svofski/library-for-ants/bloh/gripor1.jpg

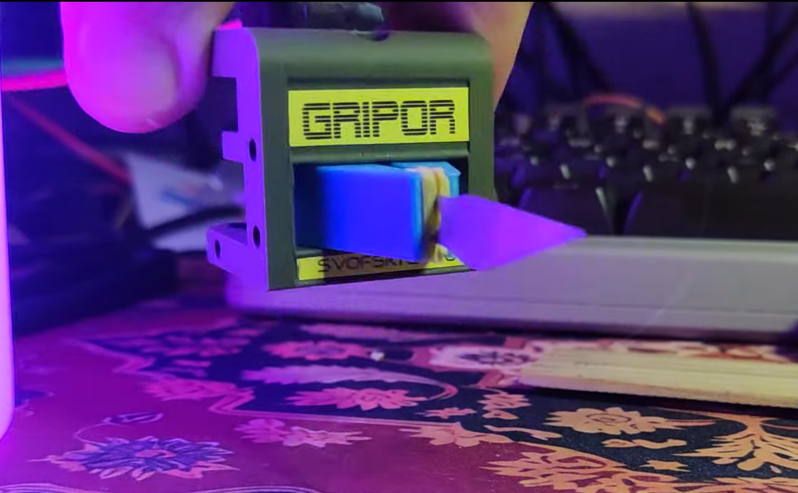
bloh/gripor1.jpg
