svofski/library-for-ants/bloh/gripor2.jpg

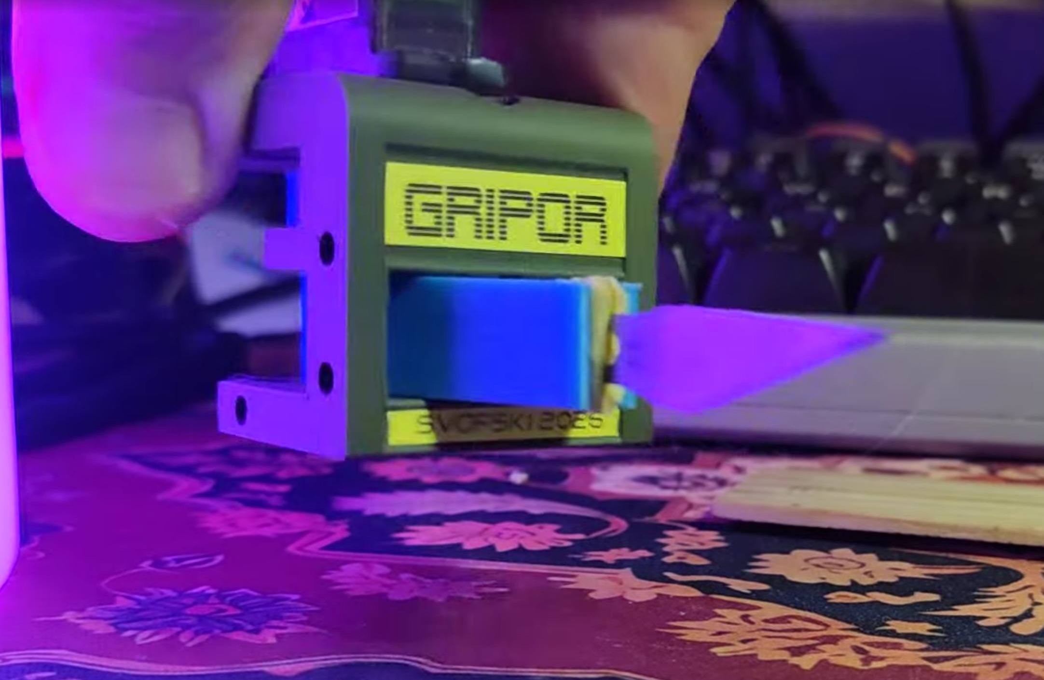
bloh/gripor2.jpg
