svofski/library-for-ants/bloh/IMG_20260404_140003.jpg

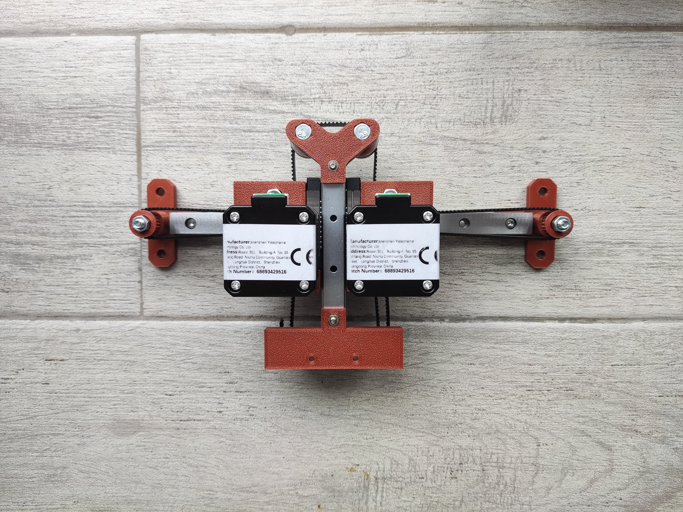
bloh/IMG_20260404_140003.jpg
