svofski/library-for-ants/bloh/IMG_20260531_192031.jpg

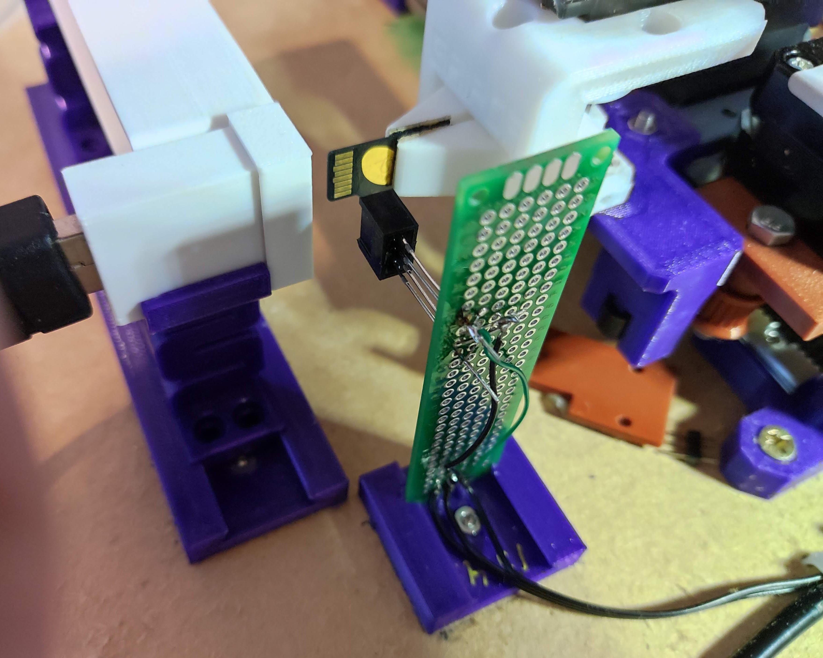
bloh/IMG_20260531_192031.jpg
