svofski/library-for-ants/bloh/IMG_20260725_130940.jpg

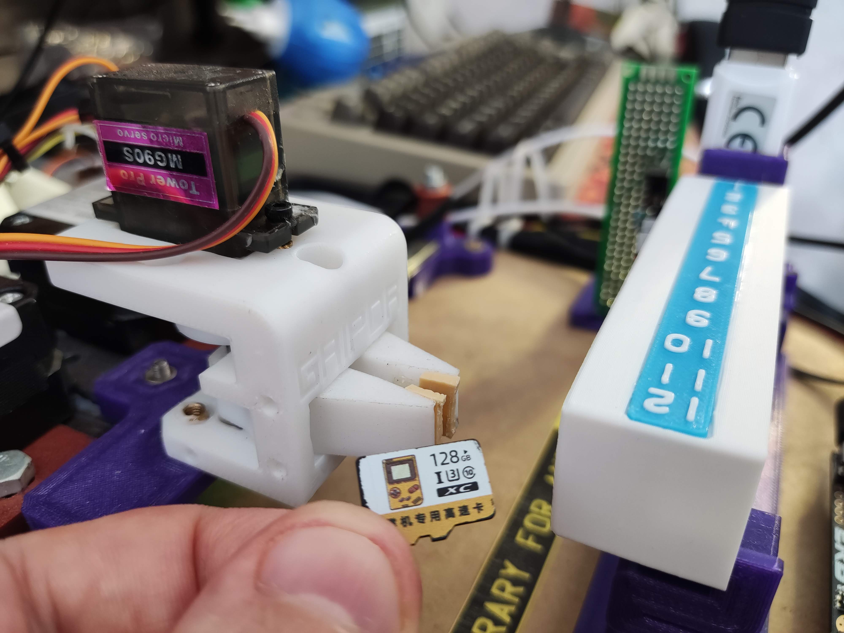
bloh/IMG_20260725_130940.jpg
