svofski/library-for-ants/bloh/pgripor.gif

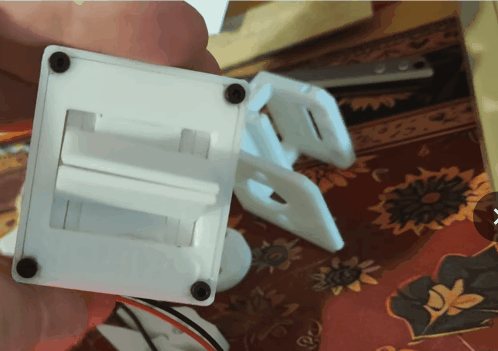
bloh/pgripor.gif
