svofski/library-for-ants/bloh/vlcsnap-2026-07-26-14h47m13s632.png

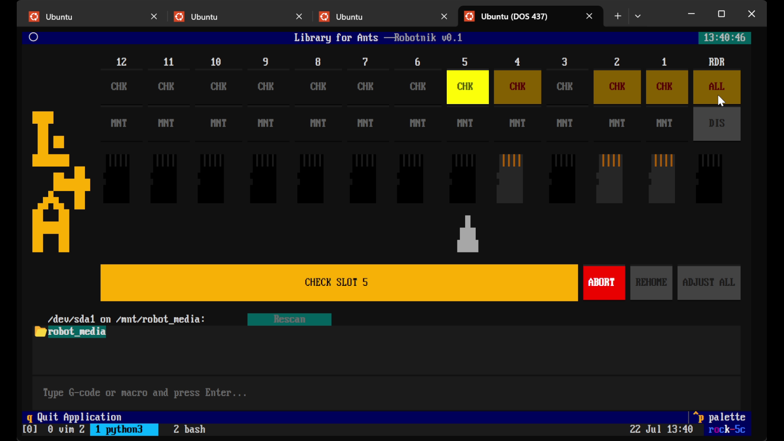
bloh/vlcsnap-2026-07-26-14h47m13s632.png
